HestiaPi/hestia-touch-pcb-dev/HestiaPi-ONE/PDF/ONE_etch_mask_bottom.pdf

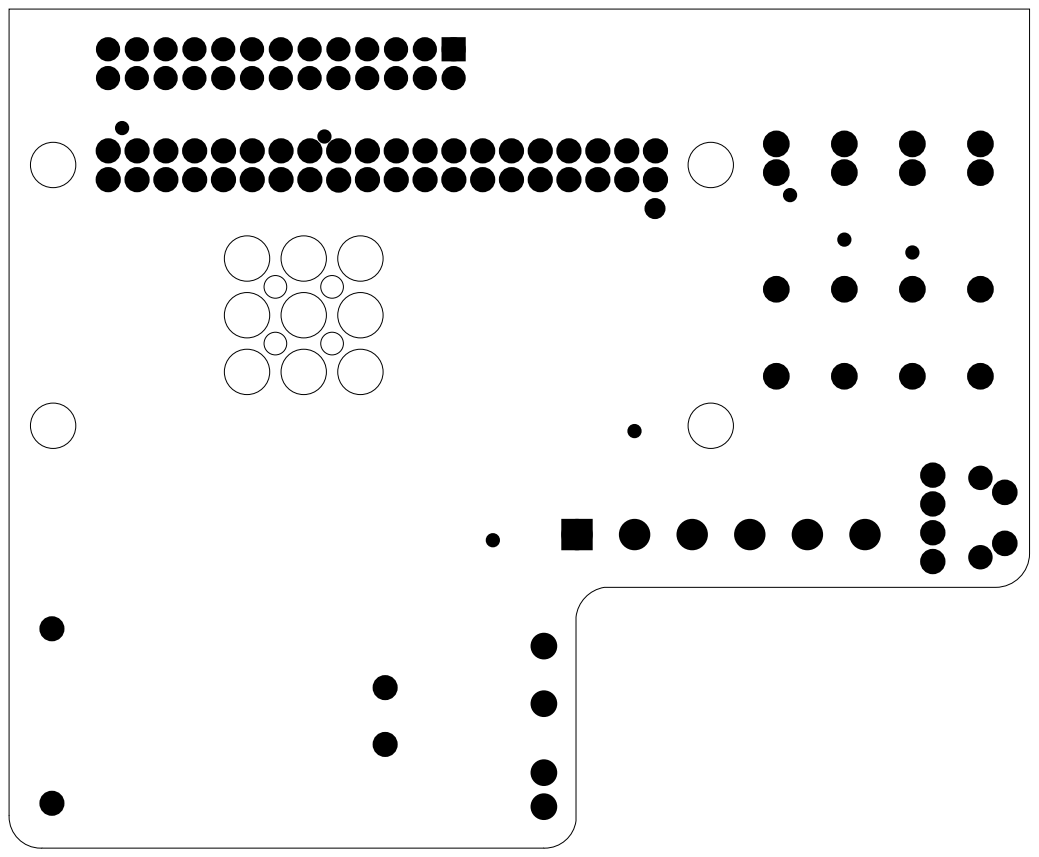
[picture p1: page 1]
