HestiaPi/hestia-touch-pcb-dev/HestiaPi-ONE/PDF/ONE_etch_mask_bottom_mirror.pdf

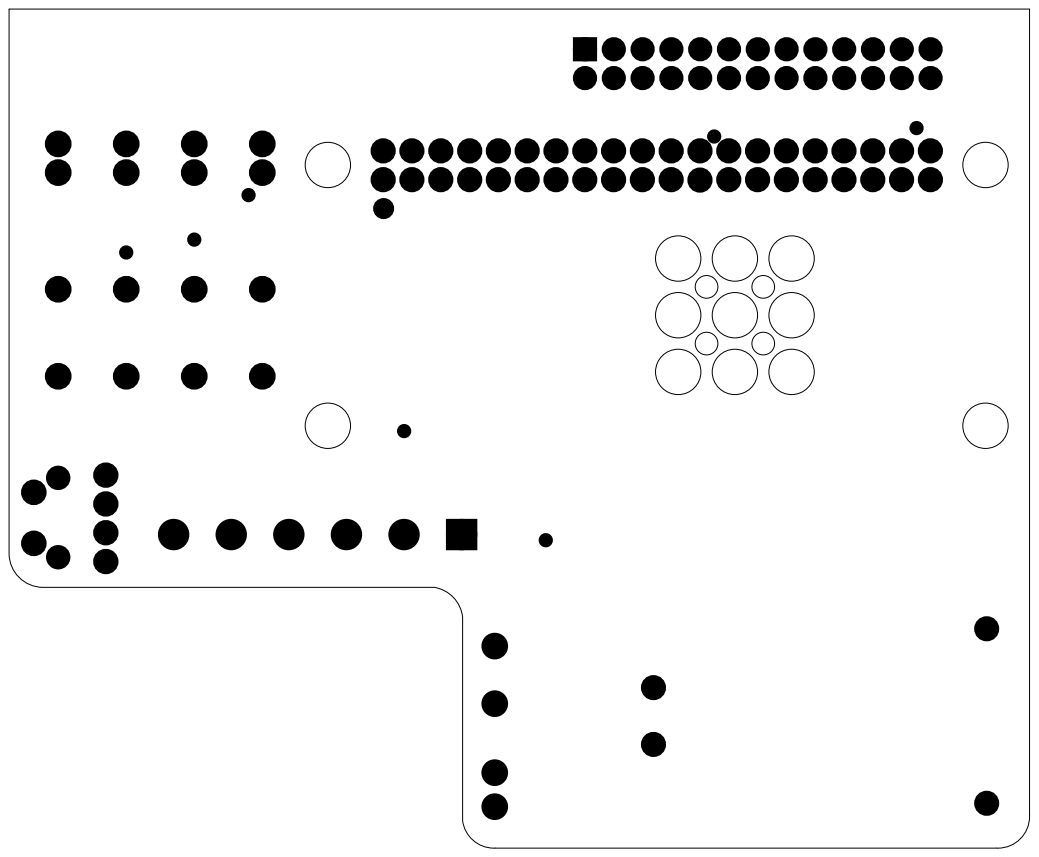
[picture p2: page 1]
