HestiaPi/hestia-touch-pcb-dev/PDF/HestiaPiTouch_etch_silk_bottom.pdf

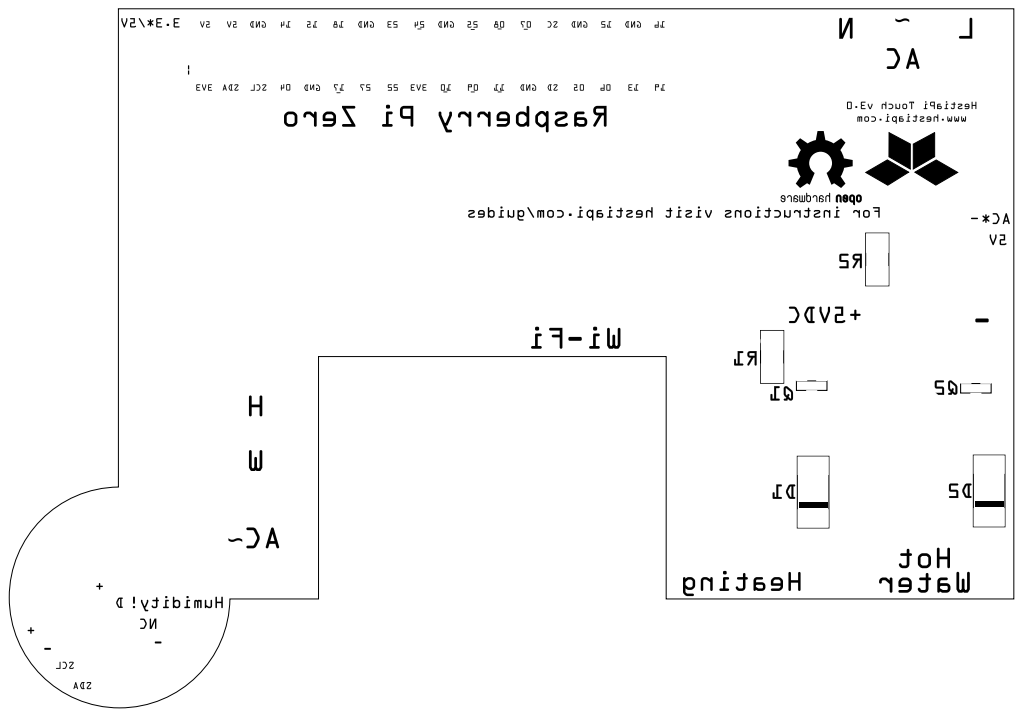
[picture p14: page 1]
