HestiaPi/hestia-touch-pcb-dev/PDF/HestiaPiTouch_etch_silk_bottom_mirror.pdf

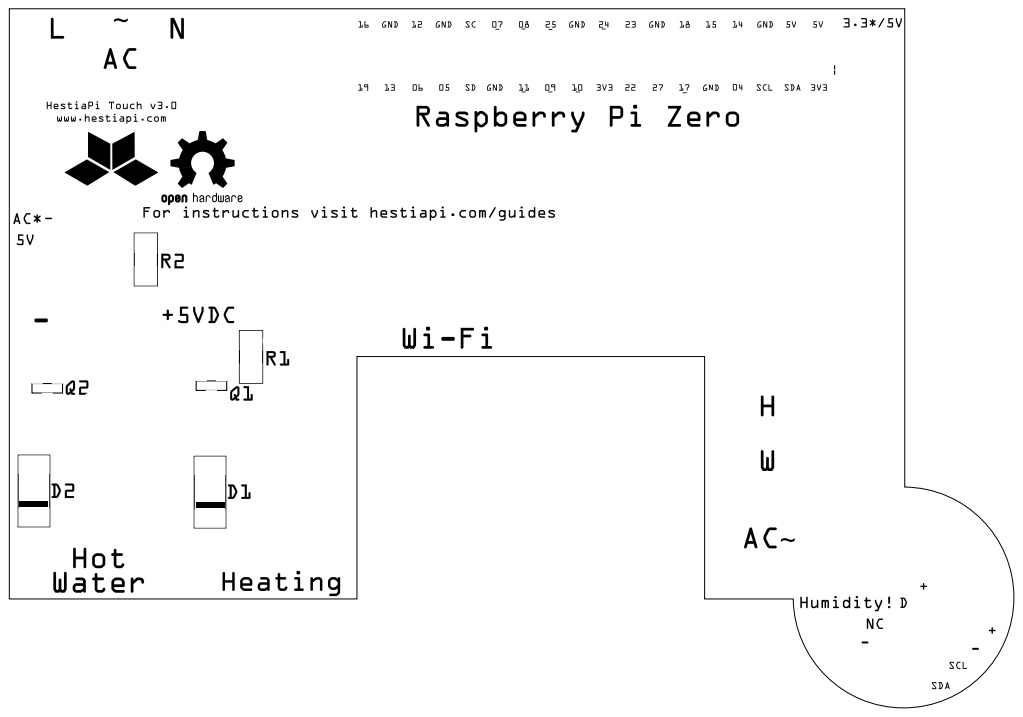
[picture p15: page 1]
