HestiaPi/hestia-touch-pcb-dev/PDF/HestiaPiTouch_etch_silk_top.pdf

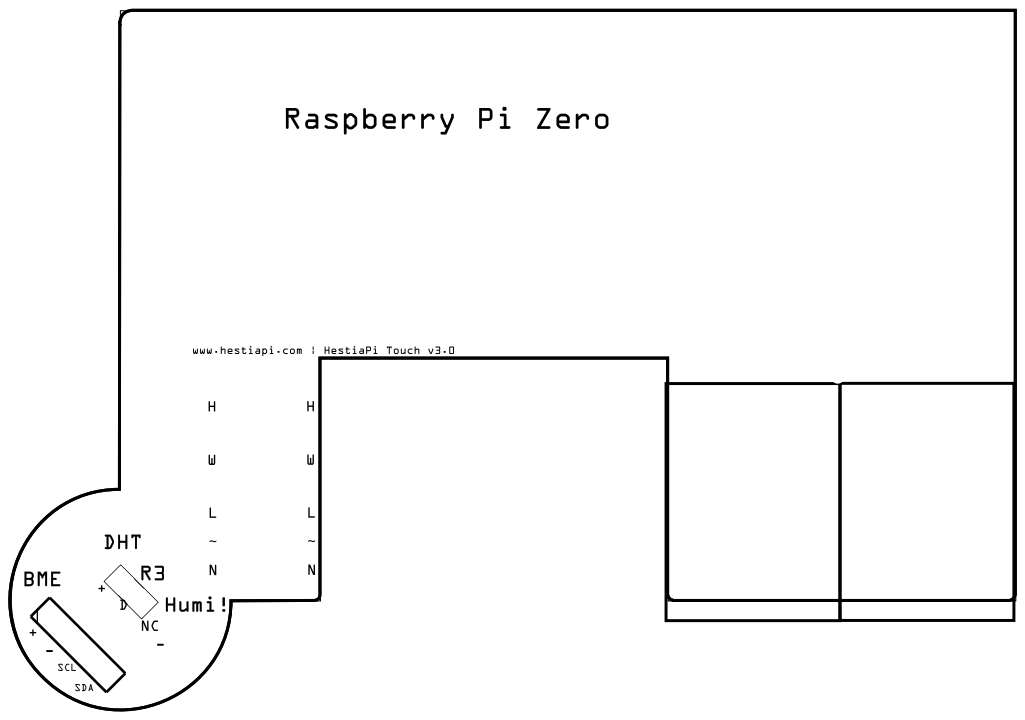
[picture p16: page 1]
