HestiaPi/hestia-touch-pcb-dev/PDF/HestiaPiTouch_etch_silk_top_mirror.pdf

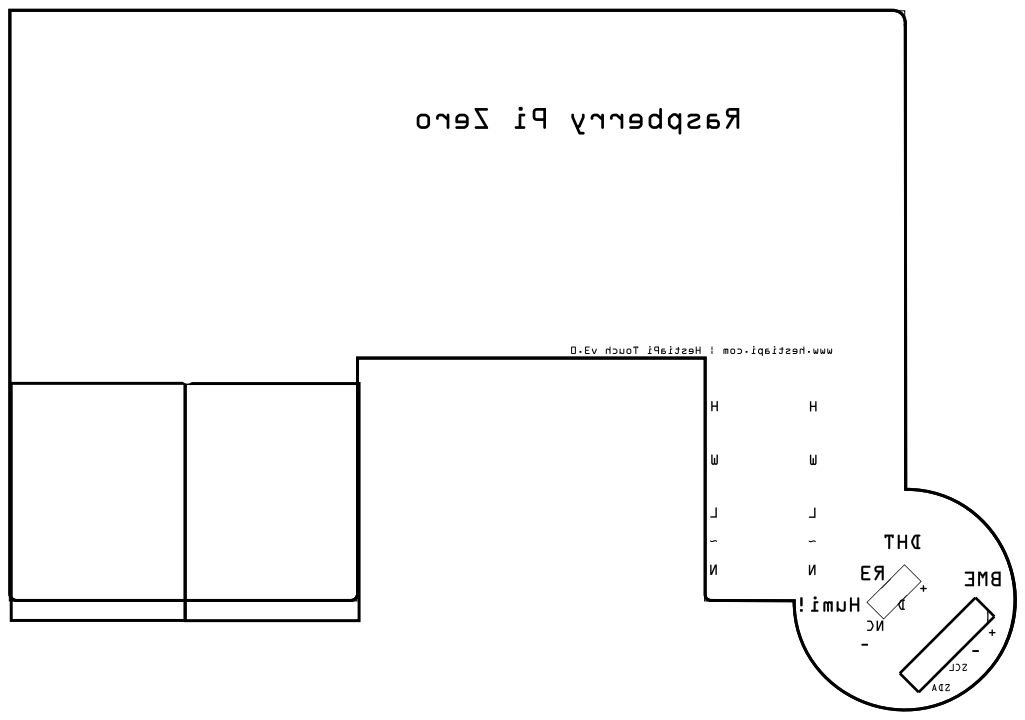
[picture p17: page 1]
