HestiaPi/hestia-touch-pcb-dev/HestiaPi-ONE/PDF/ONE_etch_copper_bottom.pdf

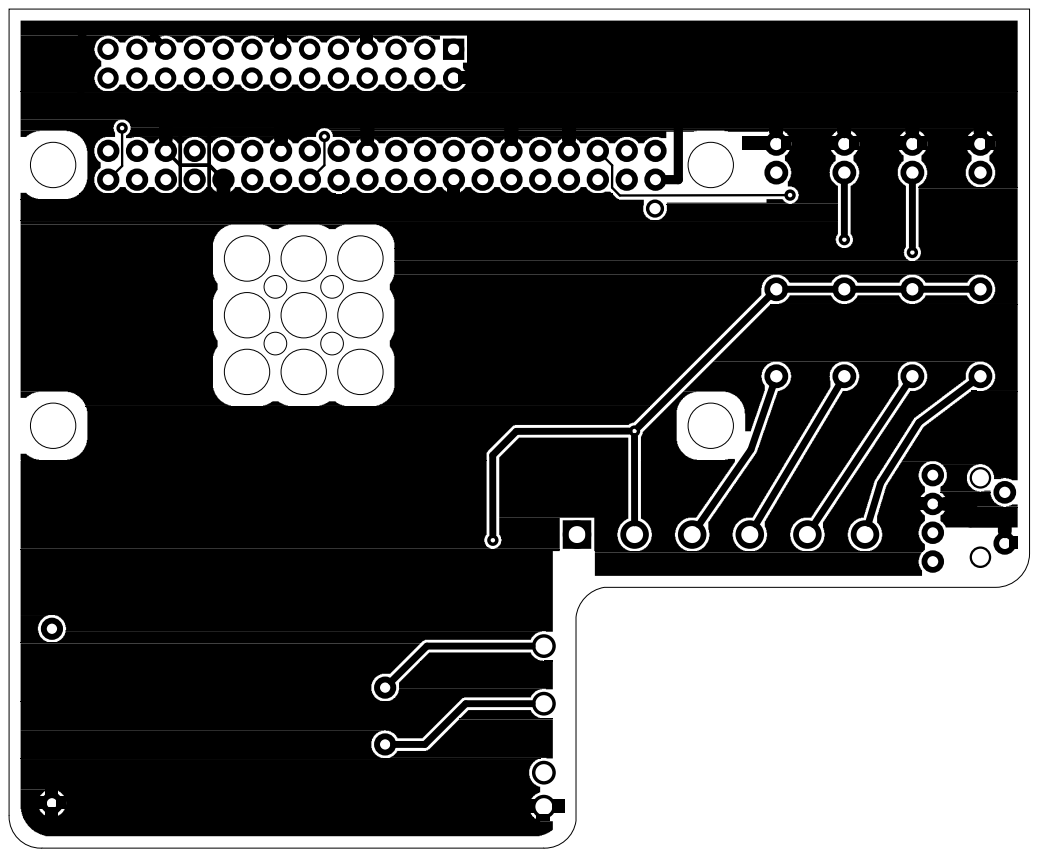
[picture p18: page 1]
