HestiaPi/hestia-touch-pcb-dev/HestiaPi-ONE/PDF/ONE_etch_copper_bottom_mirror.pdf

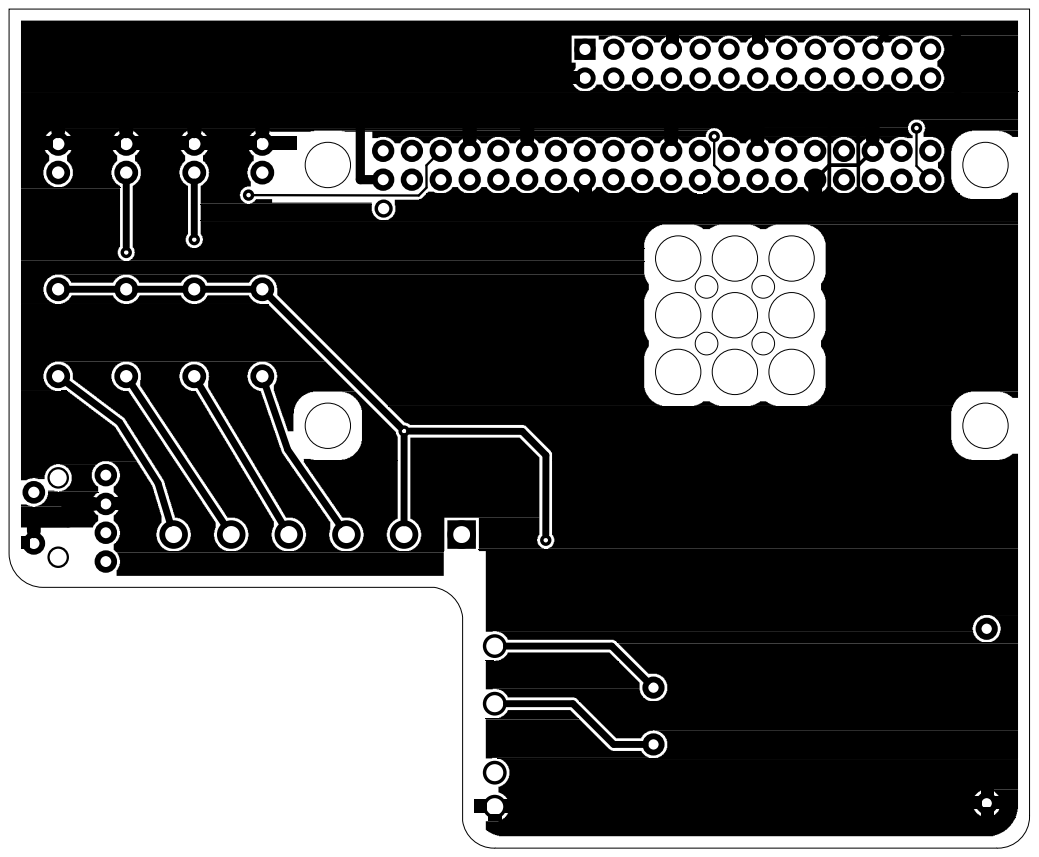
[picture p19: page 1]
