HestiaPi/hestia-touch-pcb-dev/HestiaPi-ONE/PDF/ONE_etch_copper_top.pdf

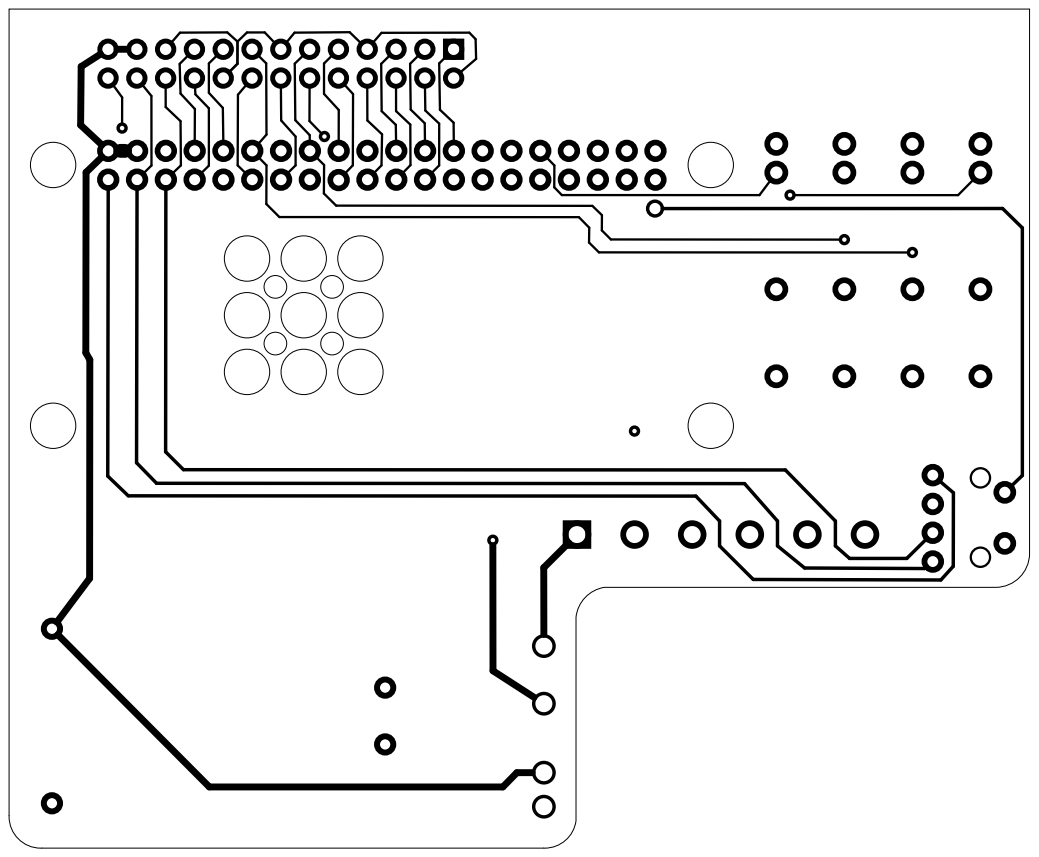
[picture p20: page 1]
