HestiaPi/hestia-touch-pcb-dev/HestiaPi-ONE/PDF/ONE_etch_copper_top_mirror.pdf

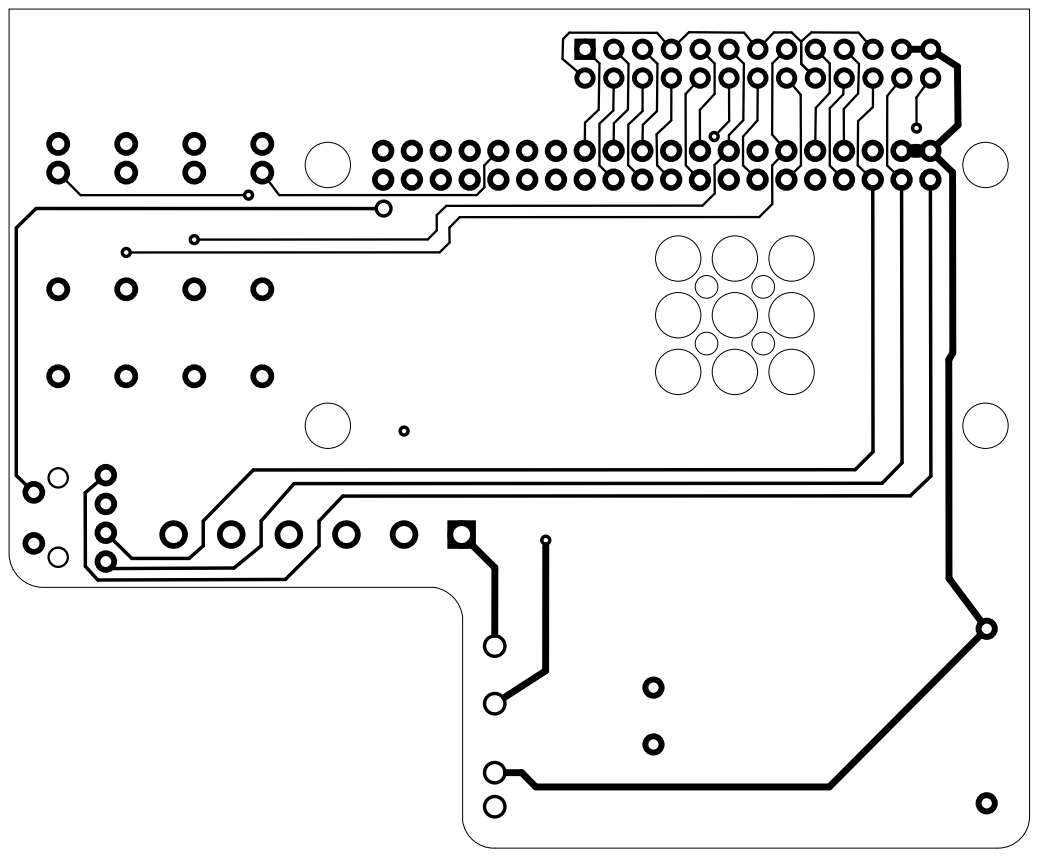
[picture p21: page 1]
