HestiaPi/hestia-touch-pcb-dev/HestiaPi-ONE/PDF/ONE_etch_silk_bottom.pdf

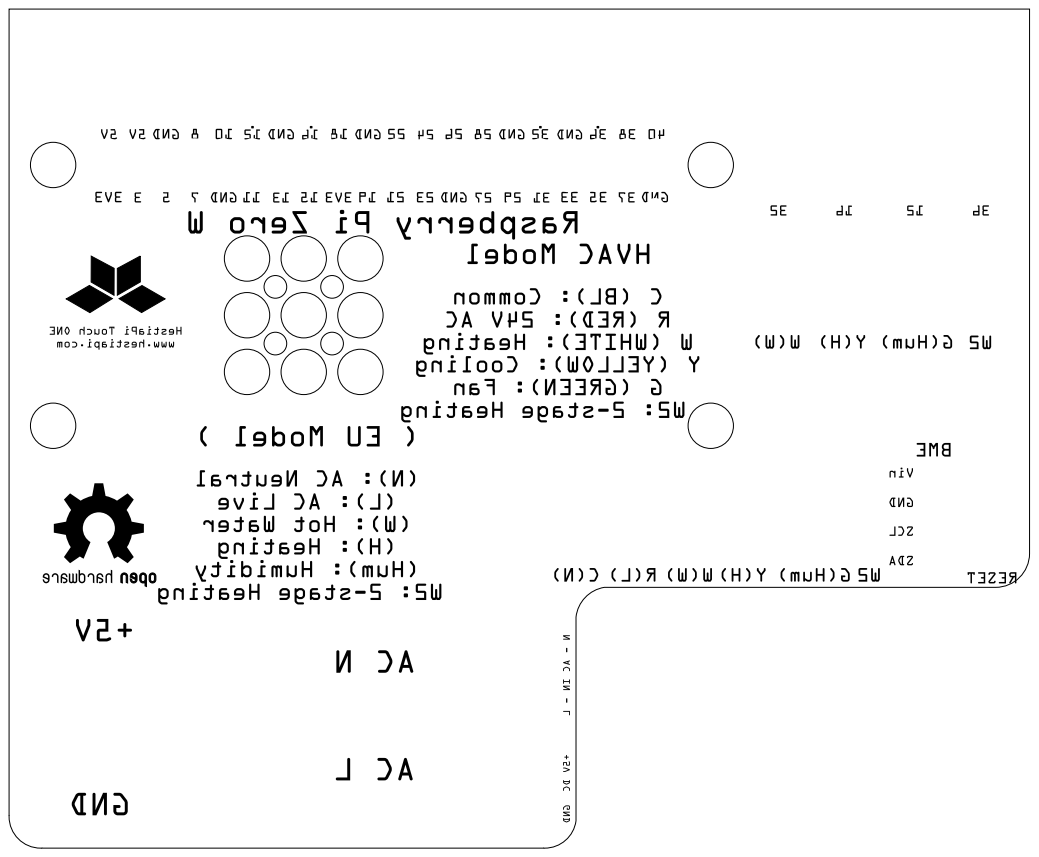
[picture p22: page 1]
