HestiaPi/hestia-touch-pcb-dev/HestiaPi-ONE/PDF/ONE_etch_silk_bottom_mirror.pdf

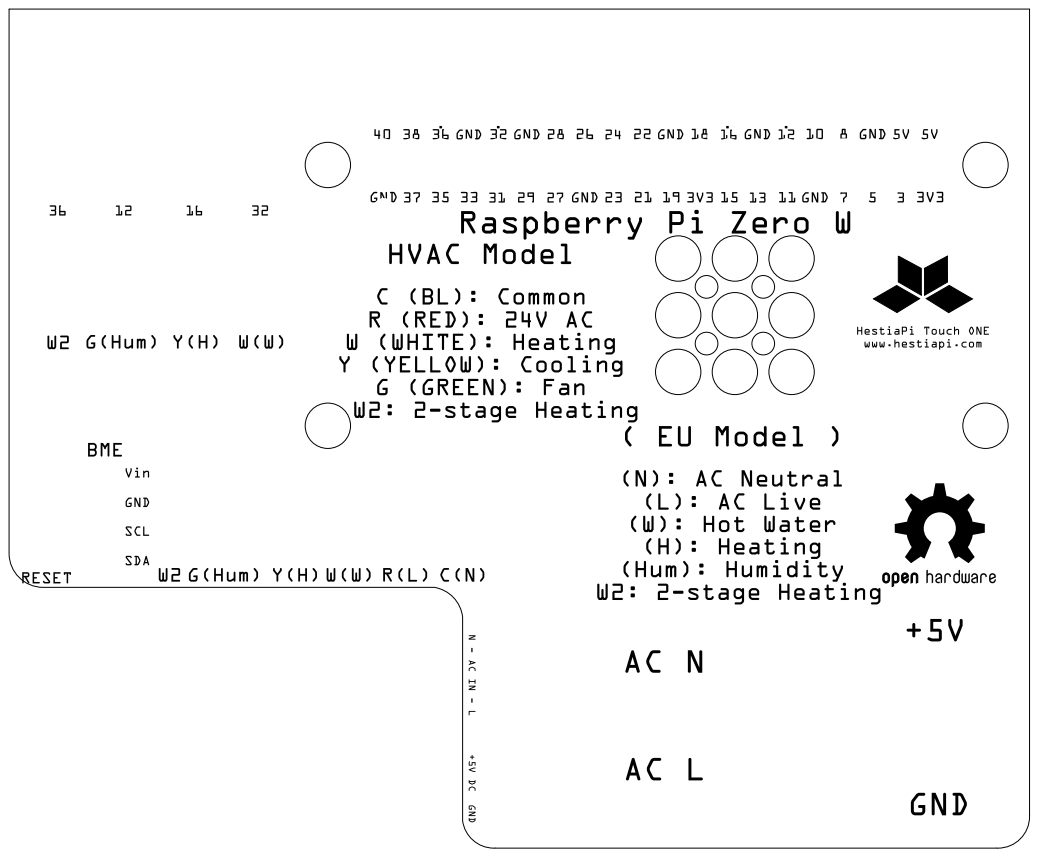
[picture p23: page 1]
