HestiaPi/hestia-touch-pcb-dev/HestiaPi-ONE/PDF/ONE_etch_silk_top.pdf

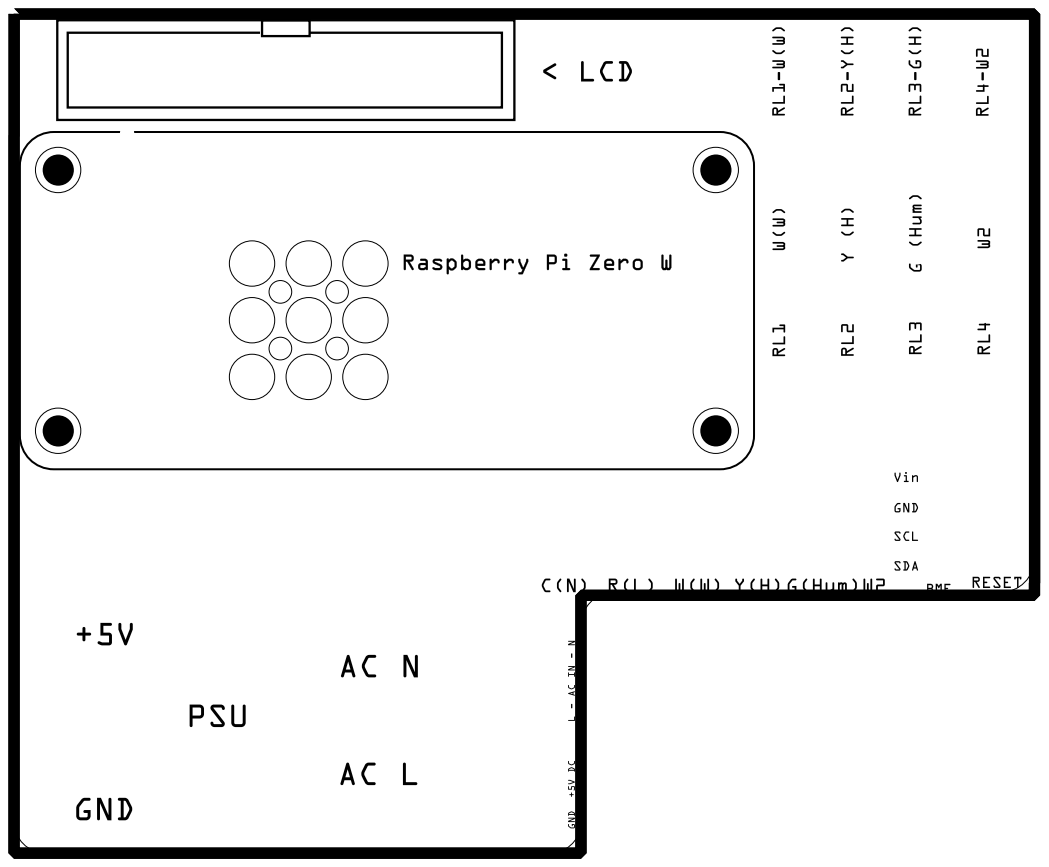
[picture p24: page 1]
