HestiaPi/hestia-touch-pcb-dev/HestiaPi-ONE/PDF/ONE_etch_silk_top_mirror.pdf

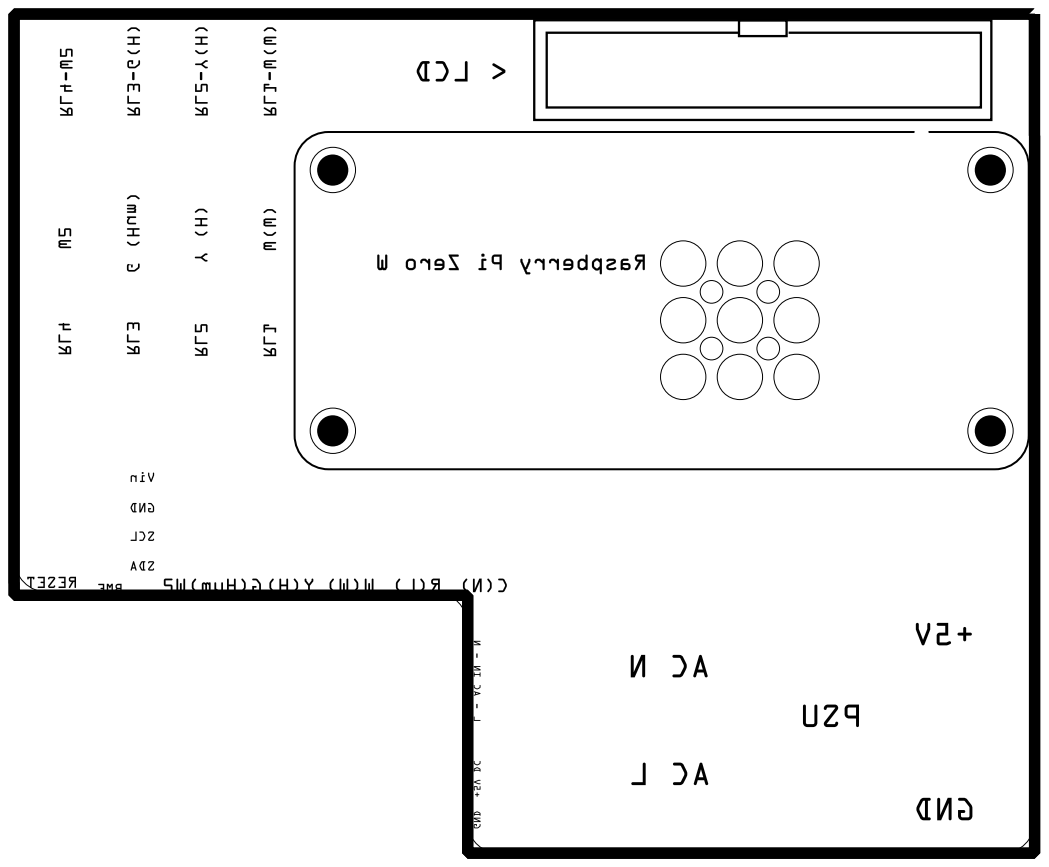
[picture p25: page 1]
