HestiaPi/hestia-touch-pcb-dev/HestiaPi-KiCAD/PDF/Layers.pdf

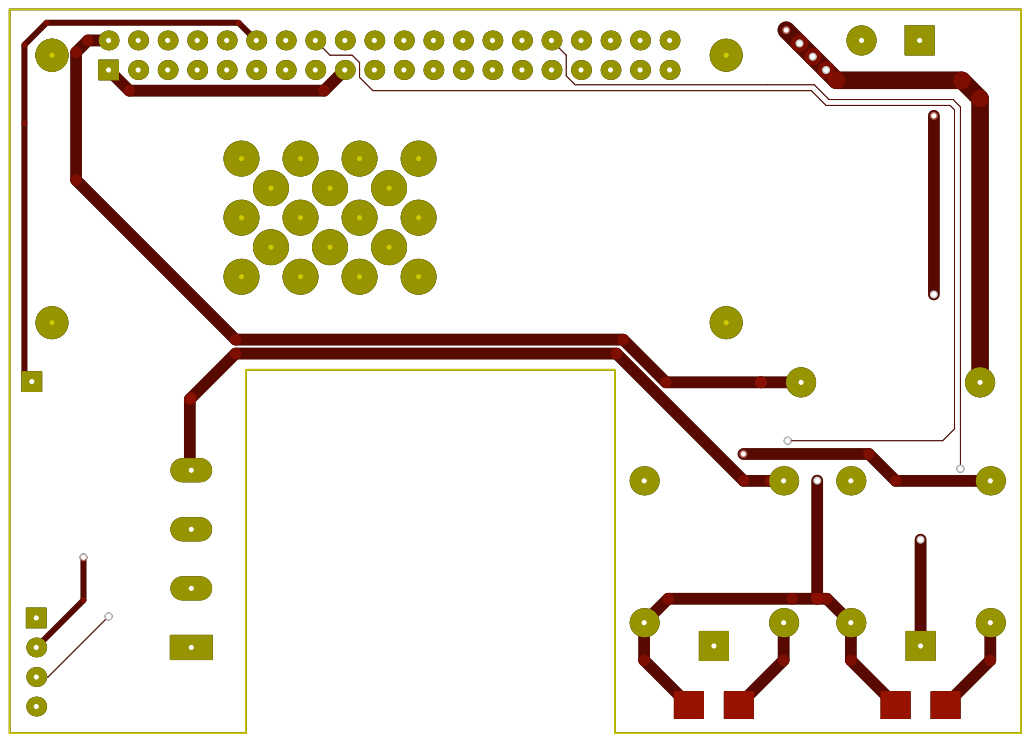
[picture p26: page 1]

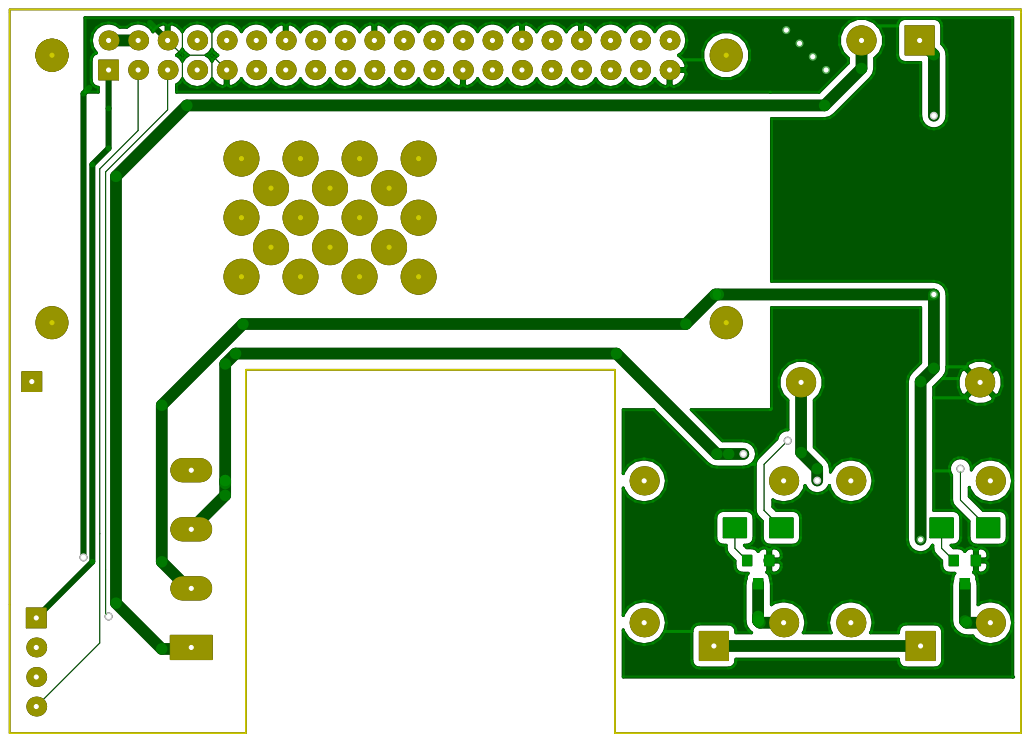
[picture p27: page 2]

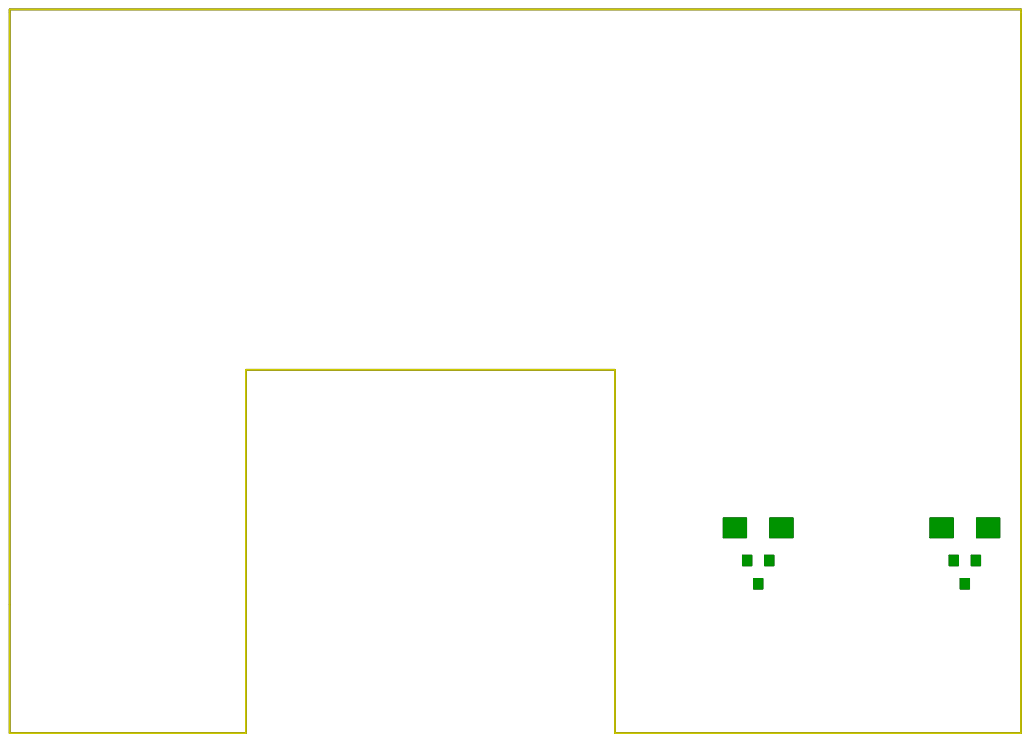
[picture p28: page 3]

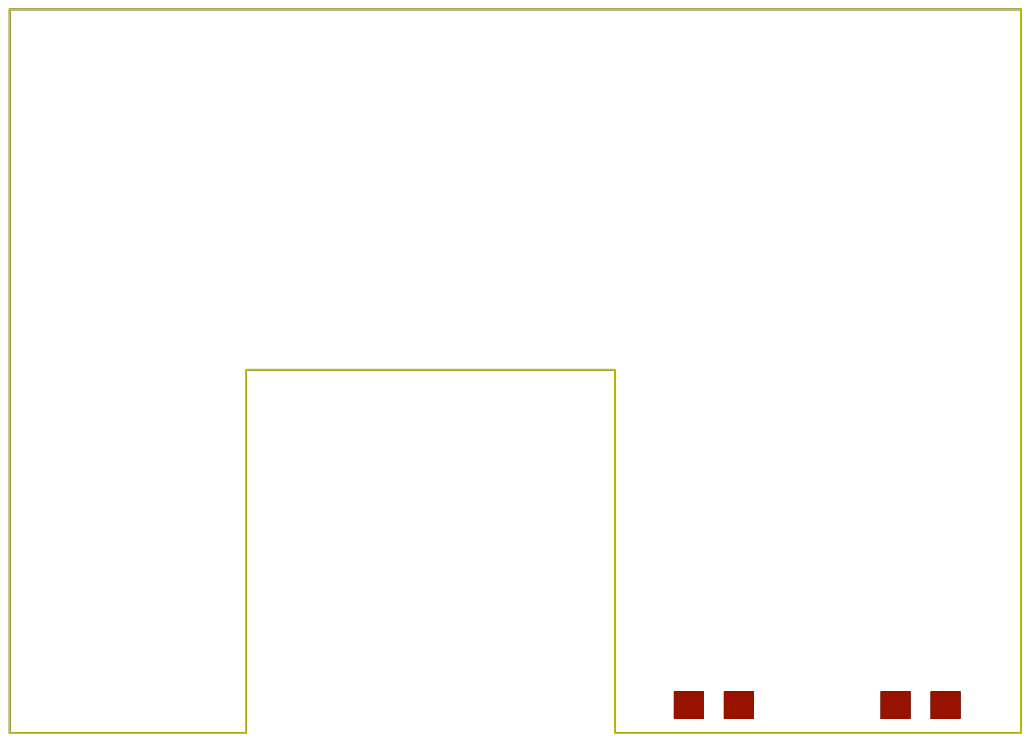
[picture p29: page 4]

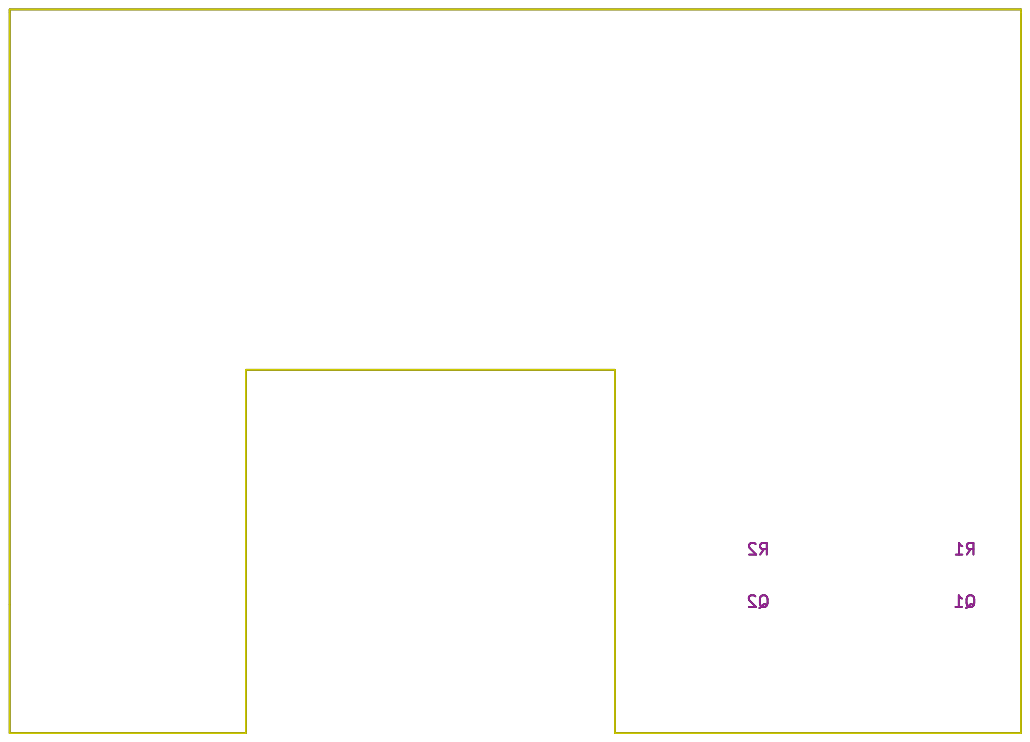
[picture p30: page 5]

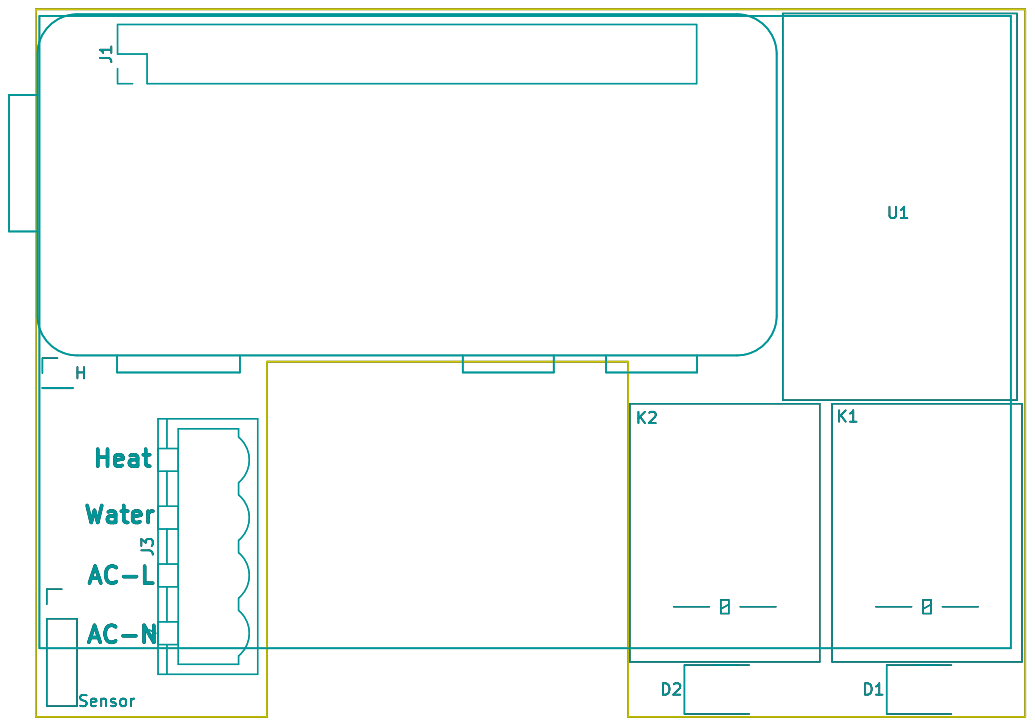
[picture p31: page 6]

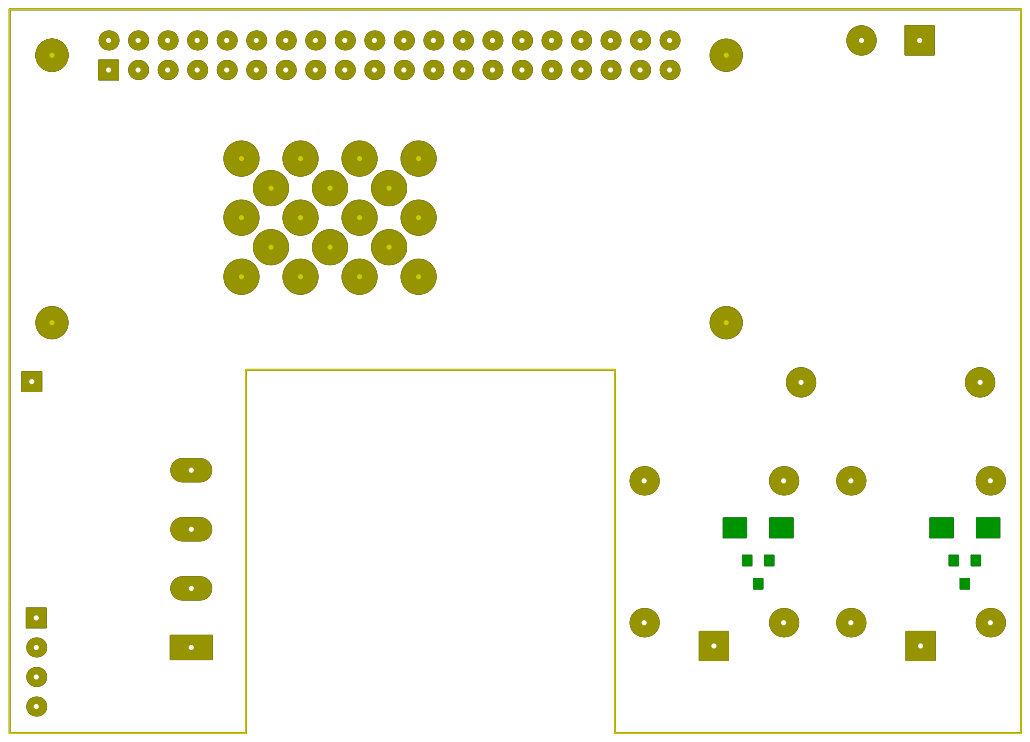
[picture p32: page 7]

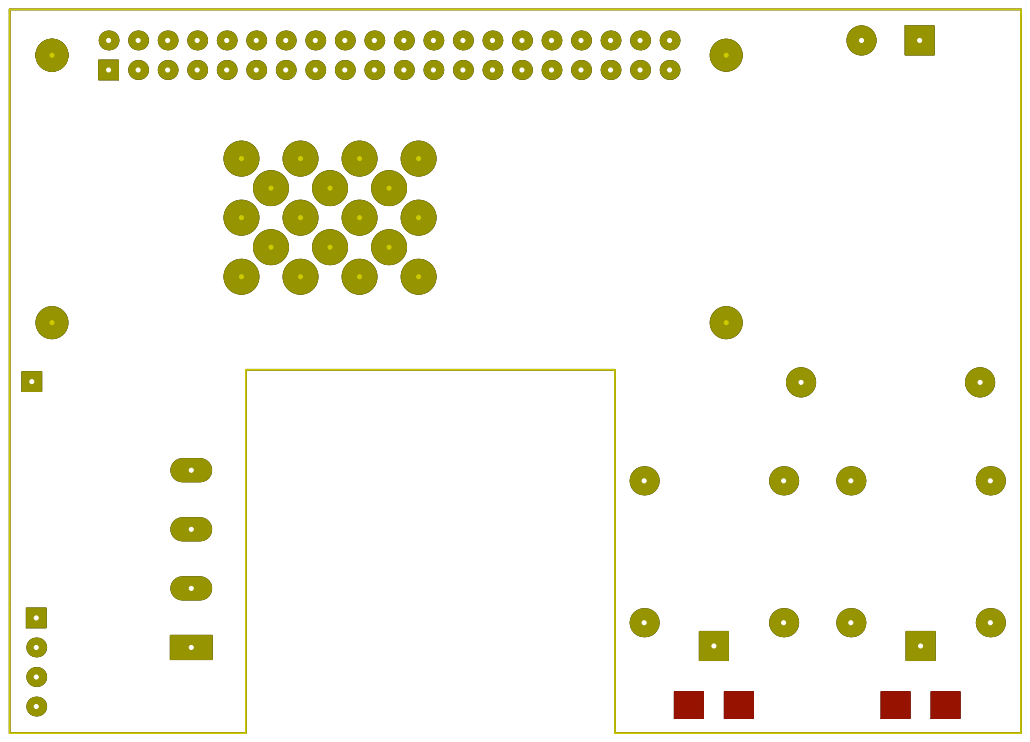
[picture p33: page 8]

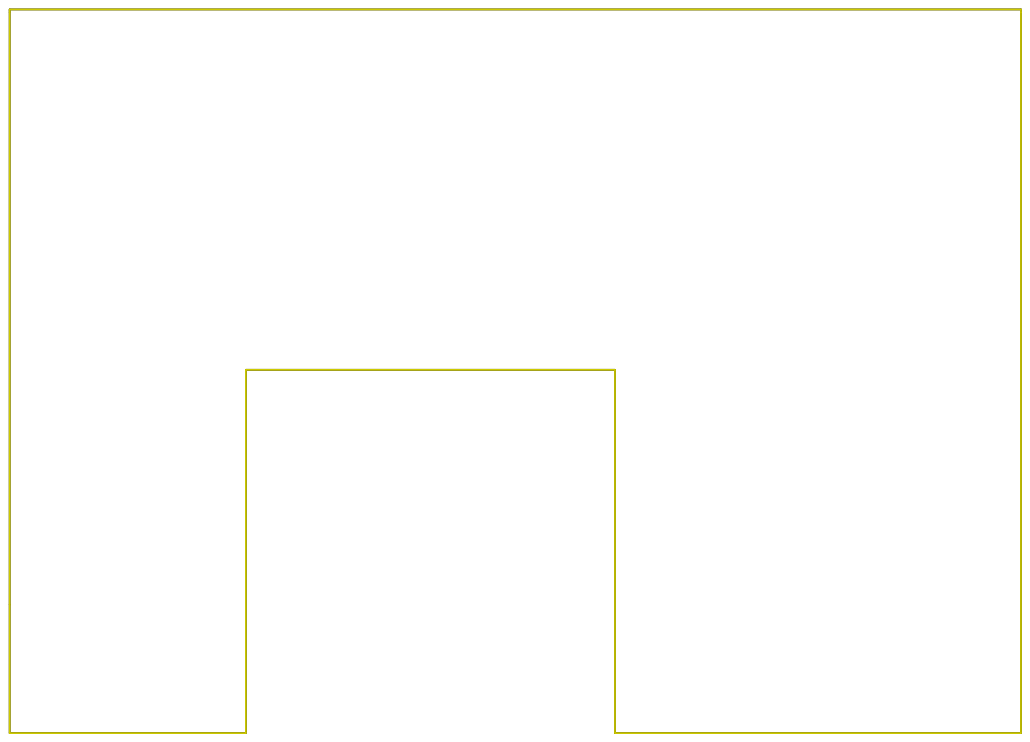
[picture p34: page 9]

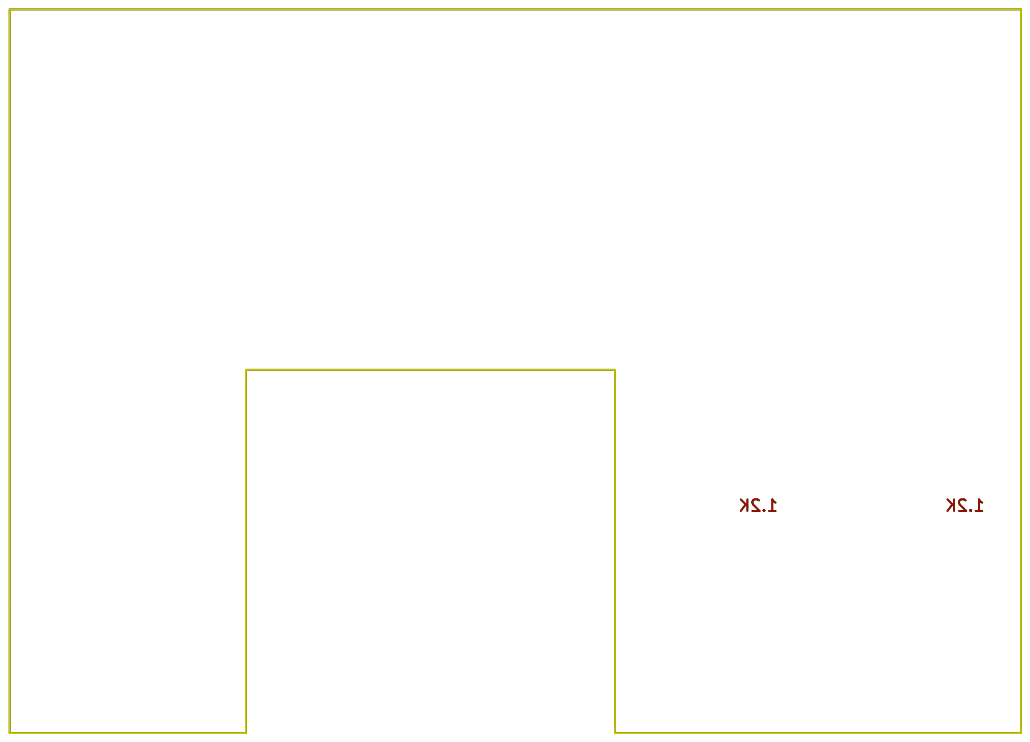
[picture p35: page 17]

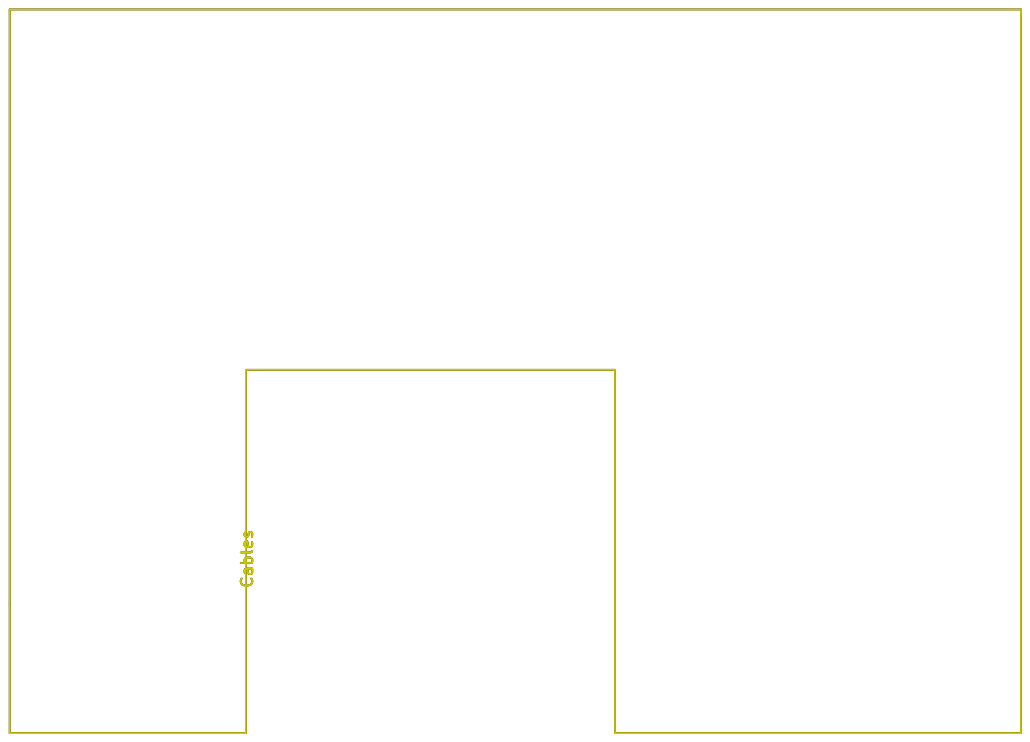
[picture p36: page 18]
